dmitrijnaprimer/MT6835_EVAL/construction/STEP/encoder-stand_plastic/encoder-stand_magnet-holder_4x2-round.STEP

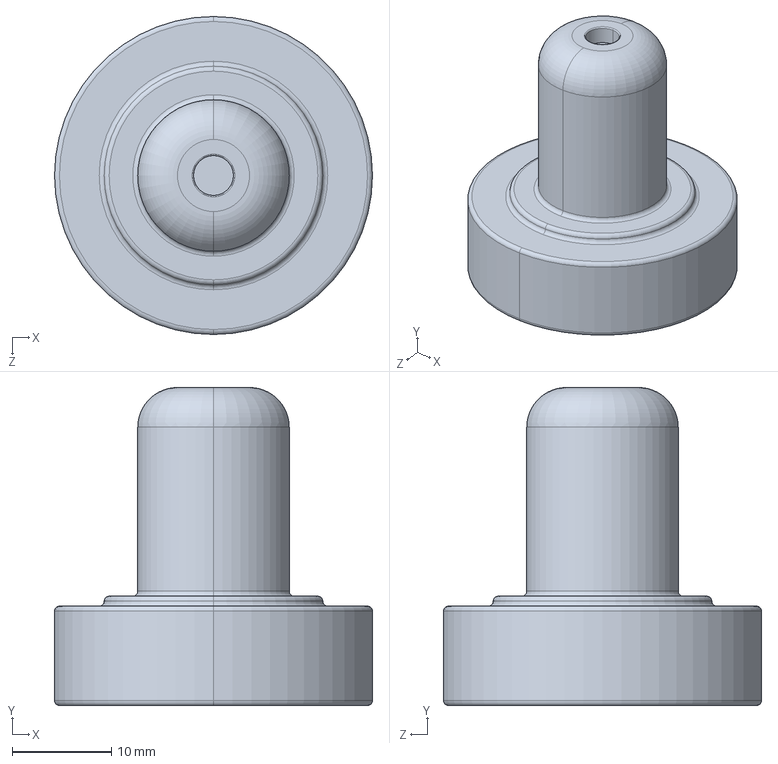
[picture p14: CAD file, 2026-03-23]
construction/STEP/encoder-stand_plastic/encoder-stand_magnet-holder_4x2-round.STEP
32.0 x 32.0 x 32.0 mm
