dmitrijnaprimer/MT6835_EVAL/construction/STEP/encoder-stand_plastic/encoder-stand_base.STEP

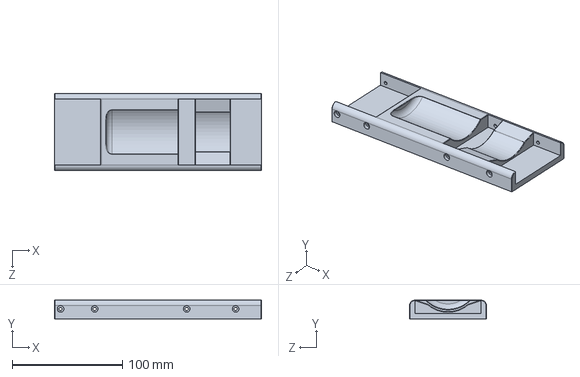
[picture p15: CAD file, 2026-03-23]
construction/STEP/encoder-stand_plastic/encoder-stand_base.STEP
188.0 x 17.0 x 70.0 mm
