dmitrijnaprimer/MT6835_EVAL/construction/STEP/encoder-stand_plastic/encoder-stand_magnet-holder_6x6-cube.STEP

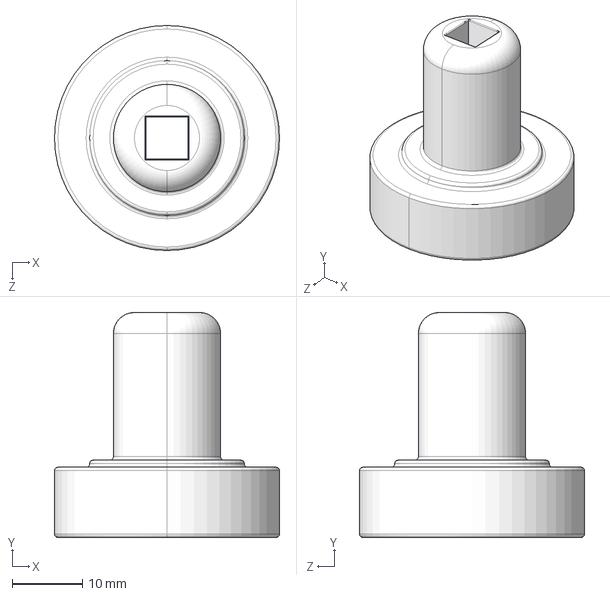
[picture p16: CAD file, 2026-03-23]
construction/STEP/encoder-stand_plastic/encoder-stand_magnet-holder_6x6-cube.STEP
32.0 x 32.0 x 32.0 mm
