dmitrijnaprimer/MT6835_EVAL/construction/STEP/encoder-stand_plastic/encoder-stand_bearing-support-base.STEP

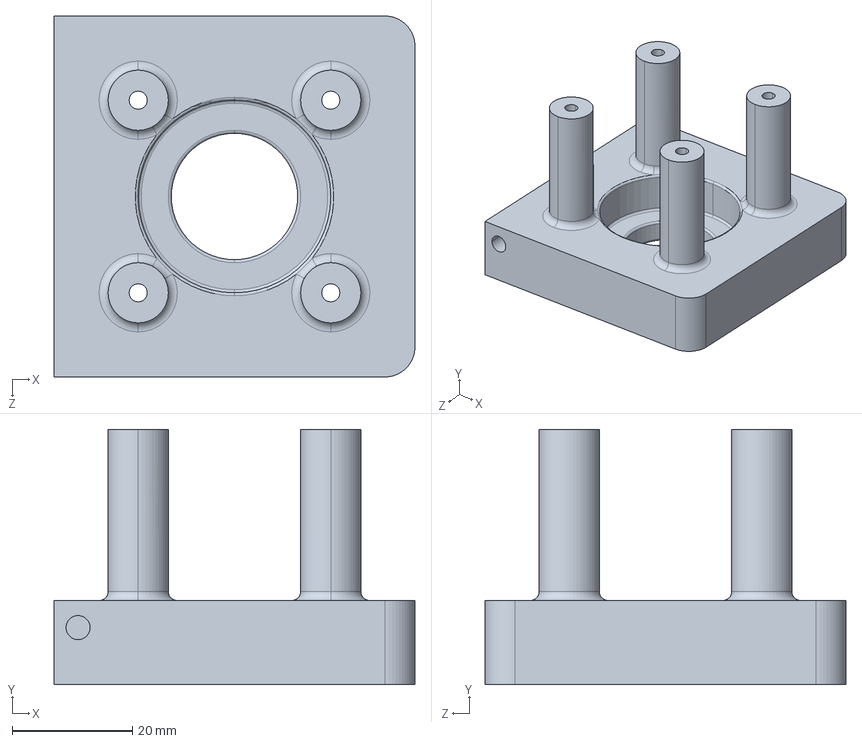
[picture p17: CAD file, 2026-03-23]
construction/STEP/encoder-stand_plastic/encoder-stand_bearing-support-base.STEP
60.0 x 42.5 x 60.0 mm
